ventilator/pixelstab/3dfiles/pixel_cylinder/inner_ring.3mf

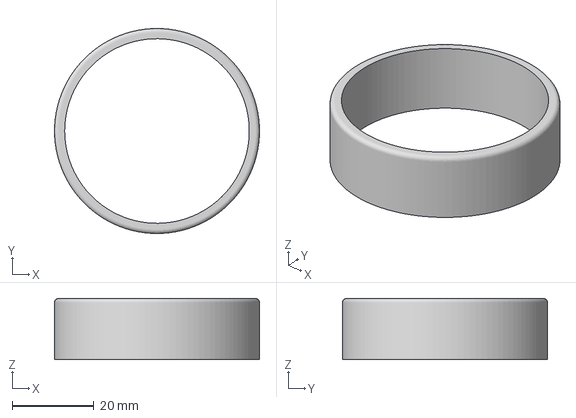
[picture p36: CAD file, 2025-04-21]
3dfiles/pixel_cylinder/inner_ring.3mf
50.2 x 50.2 x 15.0 mm
