ventilator/pixelstab/3dfiles/pixel_cylinder/variants/variant_slanted_brick_wall.3mf

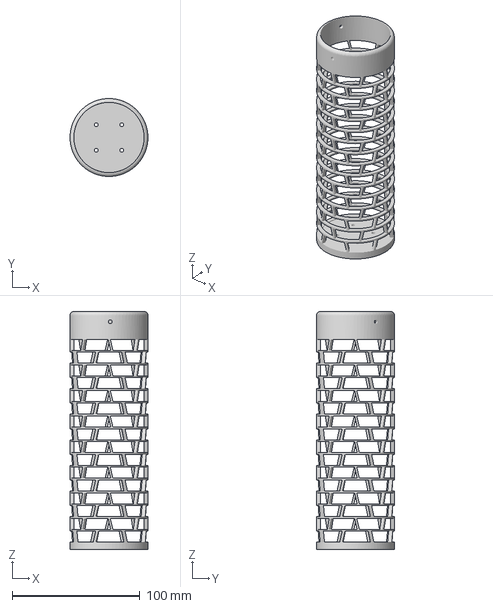
[picture p37: CAD file, 2025-04-21]
3dfiles/pixel_cylinder/variants/variant_slanted_brick_wall.3mf
60.9 x 60.9 x 186.0 mm
