ventilator/pixelstab/3dfiles/pixel_cylinder/single_pixel_right_half.3mf

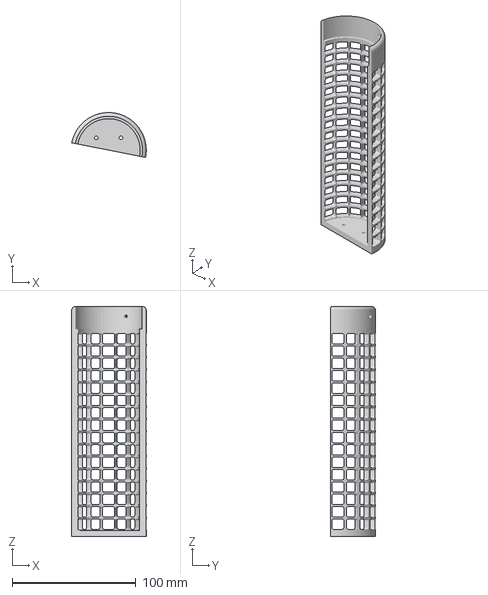
[picture p38: CAD file, 2025-04-21]
3dfiles/pixel_cylinder/single_pixel_right_half.3mf
60.3 x 36.3 x 186.0 mm
