ventilator/pixelstab/3dfiles/pixel_cylinder/top_mount.3mf

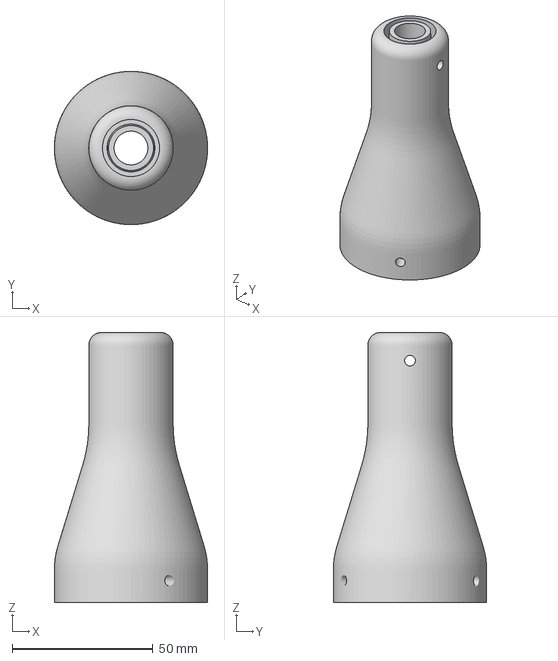
[picture p39: CAD file, 2025-04-21]
3dfiles/pixel_cylinder/top_mount.3mf
54.5 x 54.5 x 96.0 mm
