ventilator/pixelstab/3dfiles/pixel_cylinder/athom_sr_esp_holder.3mf

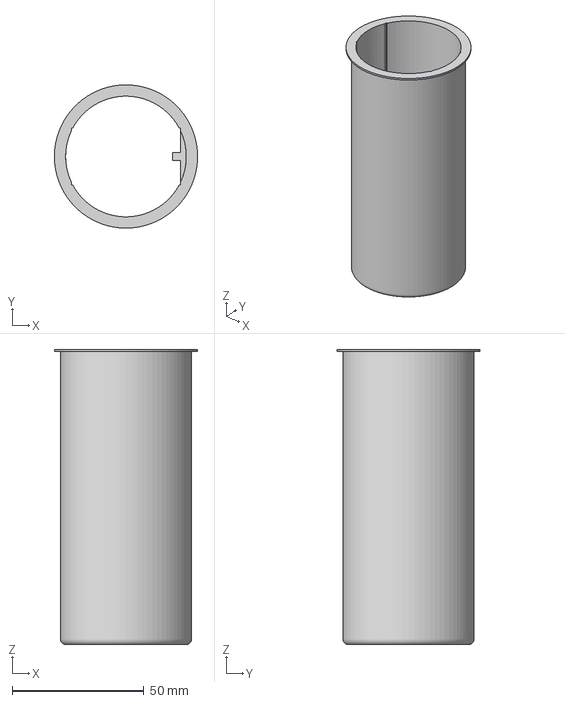
[picture p40: CAD file, 2025-04-21]
3dfiles/pixel_cylinder/athom_sr_esp_holder.3mf
54.4 x 54.4 x 112.0 mm
