ventilator/pixelstab/3dfiles/pixel_cylinder/single_pixel_left_half.3mf

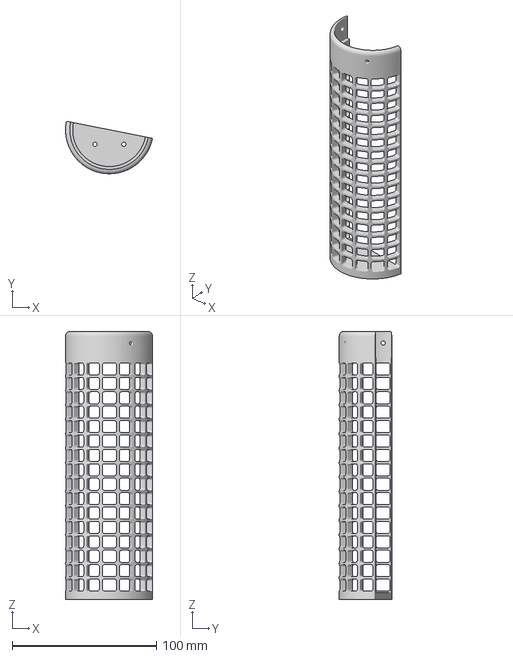
[picture p41: CAD file, 2025-04-21]
3dfiles/pixel_cylinder/single_pixel_left_half.3mf
60.4 x 36.5 x 186.0 mm
